manspaniel/digidog/src/tiles.h

#ifndef TILESET_H
#define TILESET_H

// The tile bitmap data
const uint8_t TILESET [] PROGMEM = {
  0x00, 0x00, 0x00, 0x00, 0x00, 0x00, 0x00, 0x00,
  0x00, 0x00, 0x00, 0x00, 0x00, 0x00, 0x00, 0x00,
  0x00, 0x00, 0xf0, 0xf0, 0x0e, 0xfe, 0x01, 0xff,
  0x82, 0xfe, 0x84, 0xfc, 0x08, 0xf8, 0x08, 0xf8,
  0x3e, 0xfe, 0xc1, 0xff, 0x00, 0xff, 0x00, 0xff,
  0x04, 0xff, 0x08, 0xff, 0x10, 0xff, 0x12, 0xff,
  0x04, 0xfc, 0x78, 0xf8, 0x90, 0xf0, 0x90, 0xf0,
  0x50, 0x70, 0x50, 0x70, 0x20, 0x20, 0x00, 0x00,
  0x20, 0xe0, 0x20, 0xe0, 0x20, 0xe0, 0x10, 0xf0,
  0x10, 0xf0, 0x10, 0xf0, 0xc8, 0xf8, 0x38, 0x38,
  0x00, 0xff, 0x00, 0xff, 0xf8, 0xff, 0x01, 0xff,
  0x02, 0xff, 0x02, 0xff, 0x82, 0xff, 0x80, 0xff,
  0x00, 0x00, 0x00, 0x00, 0x00, 0x00, 0x80, 0x80,
  0x40, 0xc0, 0x38, 0xf8, 0x04, 0xfc, 0x18, 0xf8,
  0x20, 0xe0, 0x10, 0xf0, 0x08, 0xf8, 0x04, 0xfc,
  0x78, 0xf8, 0x80, 0x80, 0x00, 0x00, 0x00, 0x00,
  0x00, 0x00, 0x28, 0x28, 0x50, 0x50, 0x00, 0x00,
  0x28, 0x28, 0x50, 0x50, 0x00, 0x00, 0x00, 0x00,
  0x3e, 0x3e, 0xc1, 0xff, 0x00, 0xff, 0x00, 0xff,
  0x04, 0xff, 0x08, 0xff, 0x10, 0xff, 0x12, 0xff,
  0x3e, 0xfe, 0xc1, 0xff, 0x00, 0xff, 0x00, 0xff,
  0x12, 0xff, 0x2c, 0xff, 0x18, 0xff, 0x0b, 0xff,
  0x20, 0xe0, 0x20, 0xe0, 0x20, 0xe0, 0x20, 0xe0,
  0x20, 0xe0, 0x40, 0xc0, 0x40, 0xc0, 0x40, 0xc0,
  0x20, 0xe0, 0x20, 0xe0, 0x20, 0xe0, 0x18, 0xf8,
  0x04, 0xfc, 0x78, 0xf8, 0x80, 0x80, 0x00, 0x00,
  0x20, 0xe0, 0x20, 0xe0, 0x40, 0xc0, 0x40, 0xc0,
  0x40, 0xc0, 0x80, 0x80, 0x00, 0x00, 0x00, 0x00,
  0x70, 0x70, 0x8c, 0xfc, 0xa2, 0xfe, 0x01, 0xff,
  0x80, 0xff, 0x84, 0xff, 0x40, 0xff, 0x00, 0xff,
  0x00, 0xff, 0x00, 0xff, 0x00, 0xff, 0x00, 0xff,
  0x00, 0xff, 0x03, 0xff, 0x0c, 0xfc, 0x10, 0xf0,
  0x60, 0x60, 0xd8, 0xf8, 0xd4, 0xfc, 0xb4, 0xfc,
  0xab, 0xff, 0xaa, 0xfe, 0xac, 0xfc, 0x70, 0x70,
  0x00, 0x00, 0x00, 0x00, 0xf9, 0xf9, 0x06, 0xff,
  0x00, 0xff, 0x00, 0xff, 0x80, 0xff, 0x80, 0xff,
  0x00, 0xff, 0x00, 0xff, 0x00, 0xff, 0x00, 0xff,
  0xc0, 0xff, 0x00, 0xff, 0x00, 0xff, 0x00, 0xff,
  0x00, 0xff, 0x00, 0xff, 0x00, 0xff, 0x00, 0xff,
  0x00, 0xff, 0x00, 0xff, 0x00, 0xff, 0x70, 0xff,
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
};

// Sprite: poop / 1x2 tiles / 8x16 pixels / tileset #0
const uint8_t poop [] PROGMEM = {
  0x00,
  0x01,
  0x02,
  0x08,
  0x10
};

// Sprite: stand_left / 4x4 tiles / 32x32 pixels / tileset #0
const uint8_t stand_left [] PROGMEM = {
  0x00, 0x04, 0x04,
  0x01, 0x81, 0x00, 0x00,
  0x09, 0x82, 0x0b, 0x0c,
  0x11, 0x12, 0x13, 0x14,
  0x19, 0x1a, 0x1b, 0x1c
};

// Sprite: poop_alt / 1x2 tiles / 8x16 pixels / tileset #0
const uint8_t poop_alt [] PROGMEM = {
  0x00,
  0x01,
  0x02,
  0x48,
  0x10
};

// Sprite: sitting / 10x4 tiles / 80x32 pixels / tileset #0
const uint8_t sitting [] PROGMEM = {
  0x00, 0x0a, 0x04,
  0x01, 0x81, 0x00, 0x00, 0x00, 0x00, 0x00, 0x00, 0x00, 0x00,
  0x09, 0x82, 0x0d, 0x00, 0x00, 0x00, 0x00, 0x00, 0x00, 0x00,
  0x11, 0x12, 0x15, 0x16, 0x00, 0x00, 0x00, 0x00, 0x00, 0x00,
  0x19, 0x1a, 0x1d, 0x1e, 0x00, 0x00, 0x00, 0x00, 0x00, 0x00
};

// Sprite: bone / 2x1 tiles / 16x8 pixels / tileset #0
const uint8_t bone [] PROGMEM = {
  0x00,
  0x02, 0x01,
  0x18, 0x98
};

// Sprite: stand_left_wag / 4x4 tiles / 32x32 pixels / tileset #0
const uint8_t stand_left_wag [] PROGMEM = {
  0x00, 0x04, 0x04,
  0x01, 0x81, 0x00, 0x00,
  0x09, 0x82, 0x0b, 0x04,
  0x11, 0x12, 0x13, 0x14,
  0x19, 0x1a, 0x1b, 0x1c
};

// Sprite: digging / 4x4 tiles / 32x32 pixels / tileset #0
const uint8_t digging [] PROGMEM = {
  0x00, 0x04, 0x04,
  0x06, 0x07, 0x00, 0x00,
  0x0e, 0x0f, 0x0b, 0x0c,
  0x26, 0x12, 0x13, 0x14,
  0x21, 0x1a, 0x1b, 0x1c
};

// Sprite: digging_2 / 4x4 tiles / 32x32 pixels / tileset #0
const uint8_t digging_2 [] PROGMEM = {
  0x00, 0x04, 0x04,
  0x06, 0x07, 0x00, 0x00,
  0x0e, 0x0f, 0x0b, 0x04,
  0x26, 0x12, 0x13, 0x14,
  0x19, 0x22, 0x1b, 0x1c
};

// Sprite: sitting_tongue / 4x4 tiles / 32x32 pixels / tileset #0
const uint8_t sitting_tongue [] PROGMEM = {
  0x00, 0x04, 0x04,
  0x01, 0x81, 0x00, 0x00,
  0x09, 0x8a, 0x0d, 0x00,
  0x11, 0x12, 0x15, 0x16,
  0x19, 0x1a, 0x1d, 0x1e
};

// Sprite: sitting_tongue_wag / 4x4 tiles / 32x32 pixels / tileset #0
const uint8_t sitting_tongue_wag [] PROGMEM = {
  0x00, 0x04, 0x04,
  0x01, 0x81, 0x00, 0x00,
  0x09, 0x8a, 0x0d, 0x00,
  0x11, 0x12, 0x15, 0x03,
  0x19, 0x1a, 0x1d, 0x1e
};

// Sprite: walk_facing_1 / 4x4 tiles / 32x32 pixels / tileset #0
const uint8_t walk_facing_1 [] PROGMEM = {
  0x00, 0x04, 0x04,
  0x01, 0x81, 0x00, 0x00,
  0x09, 0x82, 0x0b, 0x0c,
  0x11, 0x12, 0x13, 0x14,
  0x21, 0x1a, 0x1b, 0x24
};

// Sprite: walk_facing_2 / 4x4 tiles / 32x32 pixels / tileset #0
const uint8_t walk_facing_2 [] PROGMEM = {
  0x00, 0x04, 0x04,
  0x01, 0x81, 0x40, 0x00,
  0x09, 0x82, 0x0b, 0x04,
  0x11, 0x12, 0x13, 0x14,
  0x19, 0x22, 0x23, 0x1c
};

// Sprite: walk_forward_1 / 4x4 tiles / 32x32 pixels / tileset #0
const uint8_t walk_forward_1 [] PROGMEM = {
  0x00, 0x04, 0x04,
  0x06, 0x07, 0x00, 0x00,
  0x0e, 0x0f, 0x0b, 0x0c,
  0x11, 0x12, 0x13, 0x14,
  0x21, 0x1a, 0x1b, 0x24
};

// Sprite: walk_forward_2 / 4x4 tiles / 32x32 pixels / tileset #0
const uint8_t walk_forward_2 [] PROGMEM = {
  0x00, 0x04, 0x04,
  0x06, 0x07, 0x40, 0x00,
  0x0e, 0x0f, 0x0b, 0x04,
  0x11, 0x12, 0x13, 0x14,
  0x19, 0x22, 0x23, 0x1c
};

// Sprite: stand_bone / 4x4 tiles / 32x32 pixels / tileset #0
const uint8_t stand_bone [] PROGMEM = {
  0x00, 0x04, 0x04,
  0x01, 0x81, 0x00, 0x00,
  0x20, 0xa0, 0x0b, 0x0c,
  0x11, 0x12, 0x13, 0x14,
  0x19, 0x1a, 0x1b, 0x1c
};

// Sprite: sitting_front / 4x4 tiles / 32x32 pixels / tileset #0
const uint8_t sitting_front [] PROGMEM = {
  0x00, 0x04, 0x04,
  0x00, 0x01, 0x81, 0x00,
  0x00, 0x09, 0x89, 0x40,
  0x00, 0x17, 0x97, 0x00,
  0x00, 0x1f, 0x9f, 0x00
};

// Sprite: sitting_back / 4x4 tiles / 32x32 pixels / tileset #0
const uint8_t sitting_back [] PROGMEM = {
  0x00, 0x04, 0x04,
  0x00, 0x28, 0xa8, 0x00,
  0x00, 0x30, 0xb0, 0x40,
  0x00, 0x30, 0xb0, 0x00,
  0x00, 0x38, 0xb9, 0x00
};

// Sprite: sitting_back_2 / 4x4 tiles / 32x32 pixels / tileset #0
const uint8_t sitting_back_2 [] PROGMEM = {
  0x00, 0x04, 0x04,
  0x00, 0x28, 0xa8, 0x00,
  0x00, 0x30, 0xb0, 0x40,
  0x00, 0x30, 0xb0, 0x00,
  0x00, 0x39, 0xb8, 0x00
};

// Sprite: ball / 2x2 tiles / 16x16 pixels / tileset #0
const uint8_t ball [] PROGMEM = {
  0x00,
  0x02, 0x02,
  0x2c, 0xab,
  0x6b, 0xeb
};

// Sprite: stand_left_weirdface / 4x4 tiles / 32x32 pixels / tileset #0
const uint8_t stand_left_weirdface [] PROGMEM = {
  0x00, 0x04, 0x04,
  0x29, 0xa9, 0x00, 0x00,
  0x31, 0xb1, 0x0b, 0x0c,
  0x11, 0x12, 0x13, 0x14,
  0x19, 0x1a, 0x1b, 0x1c
};

// Sprite: icon_food / 2x2 tiles / 16x16 pixels / tileset #1
const uint8_t icon_food [] PROGMEM = {
  0x01,
  0x02, 0x02,
  0x03, 0x83,
  0x0b, 0x8b
};

// Sprite: icon_poop / 2x2 tiles / 16x16 pixels / tileset #1
const uint8_t icon_poop [] PROGMEM = {
  0x01,
  0x02, 0x02,
  0x01, 0x02,
  0x09, 0x0a
};

// Sprite: ui_progress_empty / 3x2 tiles / 24x16 pixels / tileset #1
const uint8_t ui_progress_empty [] PROGMEM = {
  0x01, 0x03, 0x02,
  0x18, 0x19, 0x98,
  0x20, 0x21, 0xa0
};

// Sprite: ui_selection_arrow / 1x1 tiles / 8x8 pixels / tileset #1
const uint8_t ui_selection_arrow [] PROGMEM = {
  0x01,
  0x01,
  0x01,
  0x11
};

// Sprite: ui_menu_frame / 16x8 tiles / 128x64 pixels / tileset #1
const uint8_t ui_menu_frame [] PROGMEM = {
  0x01, 0x10, 0x08,
  0x30, 0x31, 0x31, 0x31, 0x31, 0x31, 0x31, 0x32, 0x31, 0x31, 0x31, 0x31, 0x31, 0x31, 0x31, 0xb0,
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
  0x02, 0x04, 0x04,
  0x01, 0x02, 0x02, 0x81,
  0x0d, 0x00, 0x00, 0xcd,
  0x0d, 0x00, 0x00, 0x8d,
  0x41, 0x42, 0x42, 0xc1
};

// Sprite: ui_selection_arrow_alt / 1x1 tiles / 8x8 pixels / tileset #1
const uint8_t ui_selection_arrow_alt [] PROGMEM = {
  0x01,
  0x01,
  0x01,
  0x10
};

#endif
